JefersonHernandez00/Sistema-Nivel-Y-Temperatura/img y video/ensamblaje 2.JPG

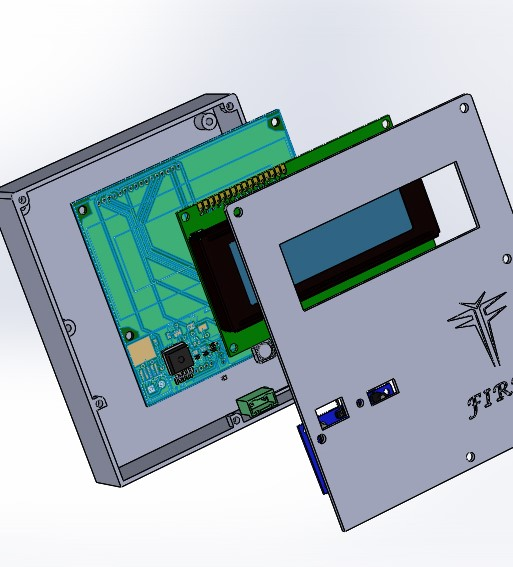
img y video/ensamblaje 2.JPG
