JefersonHernandez00/Sistema-Nivel-Y-Temperatura/img y video/Ensamblaje carcasa t.jpg

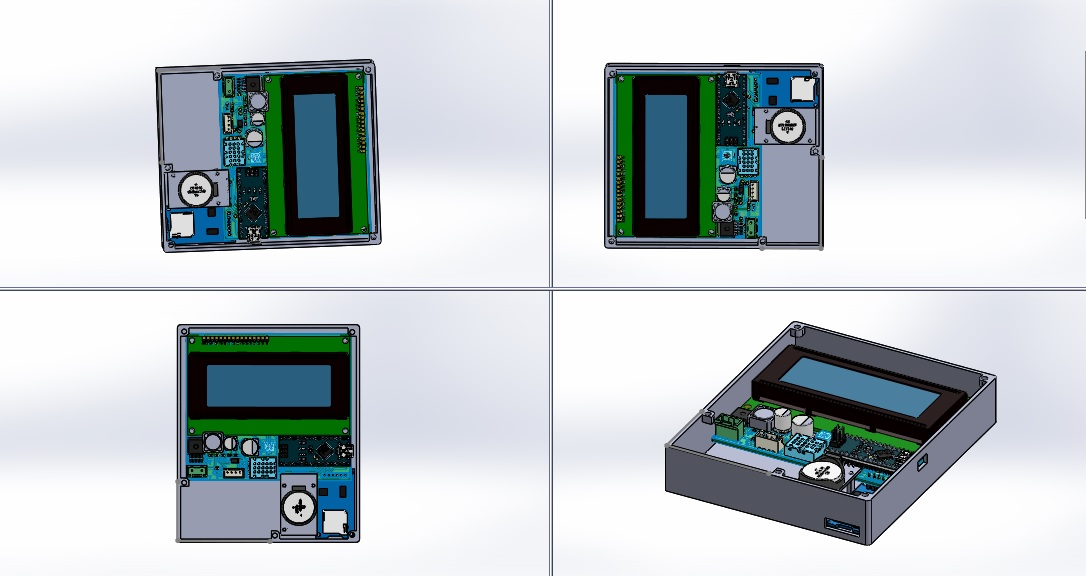
img y video/Ensamblaje carcasa t.jpg
