JefersonHernandez00/Sistema-Nivel-Y-Temperatura/img y video/.png

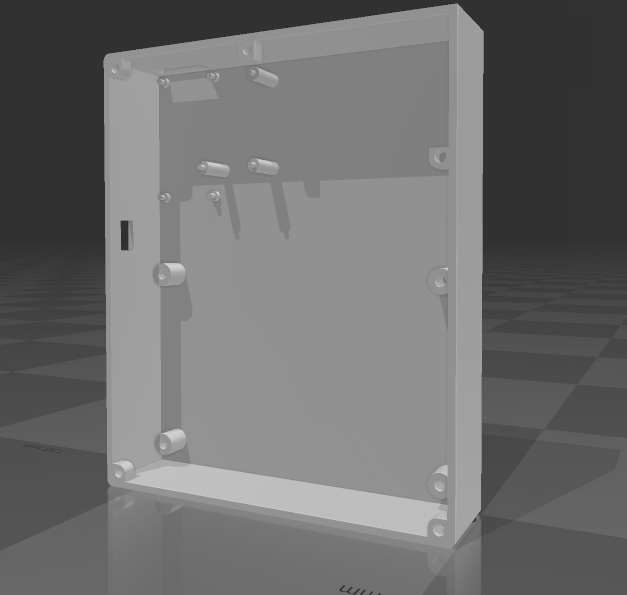
img y video/.png
