JefersonHernandez00/Sistema-Nivel-Y-Temperatura/img y video/Carcasa medidor de  nivel t.jpg

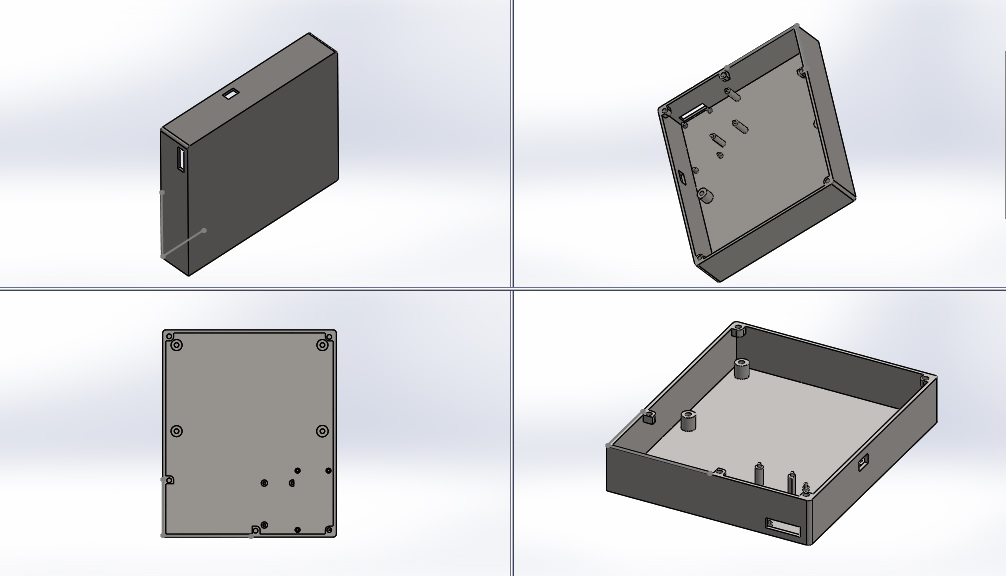
img y video/Carcasa medidor de nivel t.jpg
