JefersonHernandez00/Sistema-Nivel-Y-Temperatura/img y video/Carcasa medidor de  nivel.JPG

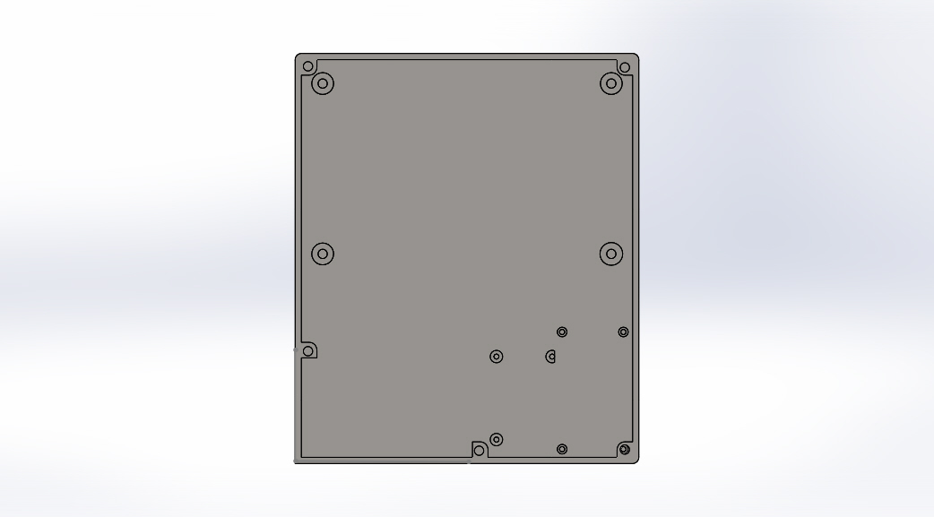
img y video/Carcasa medidor de nivel.JPG
