JefersonHernandez00/Sistema-Nivel-Y-Temperatura/img y video/cc.JPG

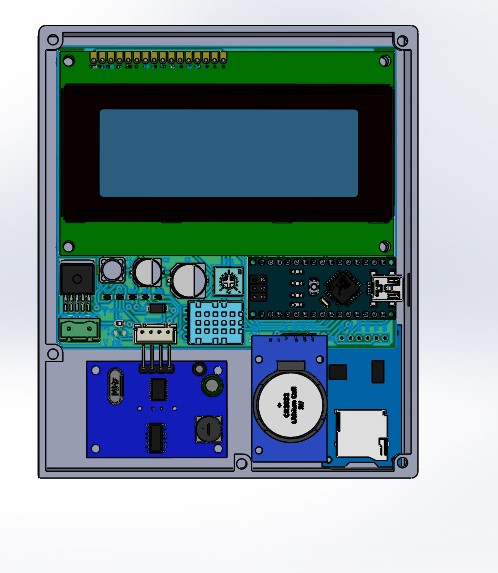
img y video/cc.JPG
