JefersonHernandez00/Sistema-Nivel-Y-Temperatura/img y video/esquematico.png

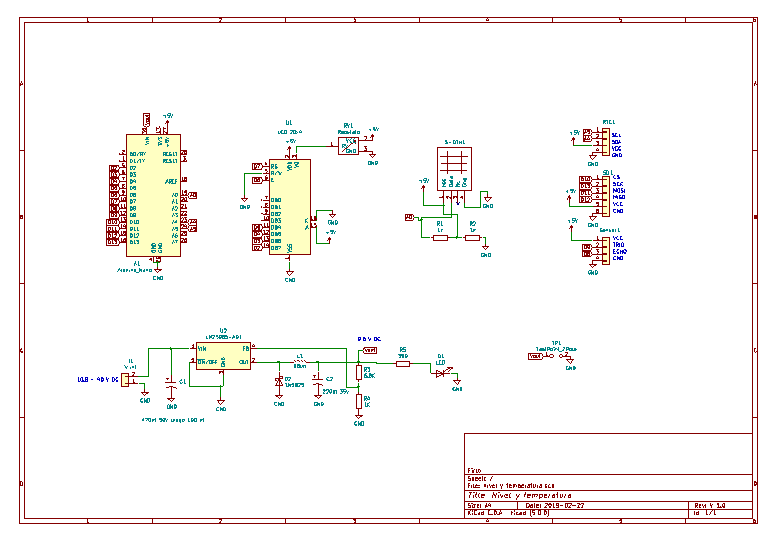
img y video/esquematico.png
