JefersonHernandez00/Sistema-Nivel-Y-Temperatura/img y video/IMG-20190923-WA0002.jpeg

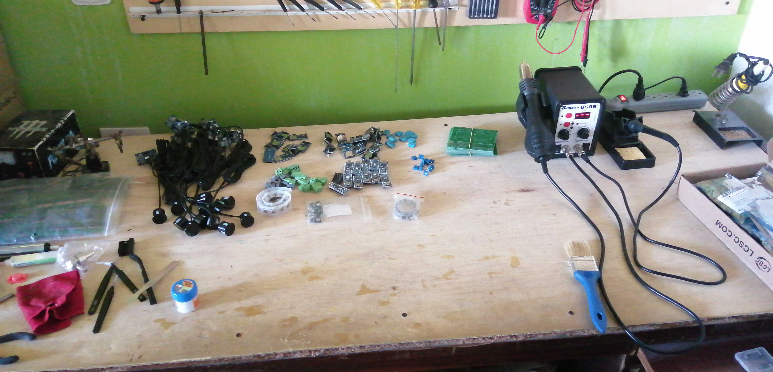
img y video/IMG-20190923-WA0002.jpeg
