JefersonHernandez00/Sistema-Nivel-Y-Temperatura/img y video/IMG-20190927-WA0010.jpg

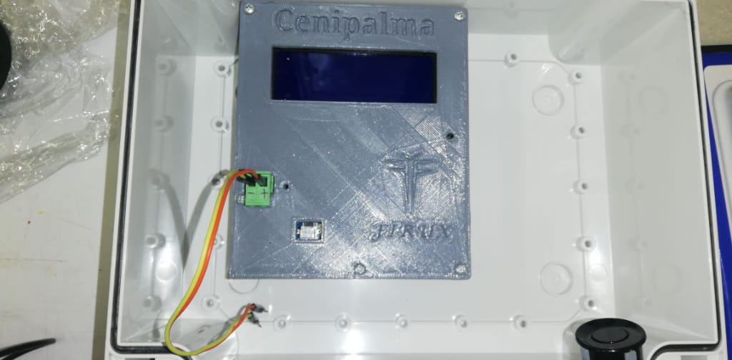
img y video/IMG-20190927-WA0010.jpg
