JefersonHernandez00/Sistema-Nivel-Y-Temperatura/img y video/IMG-20191017-WA0028.jpg

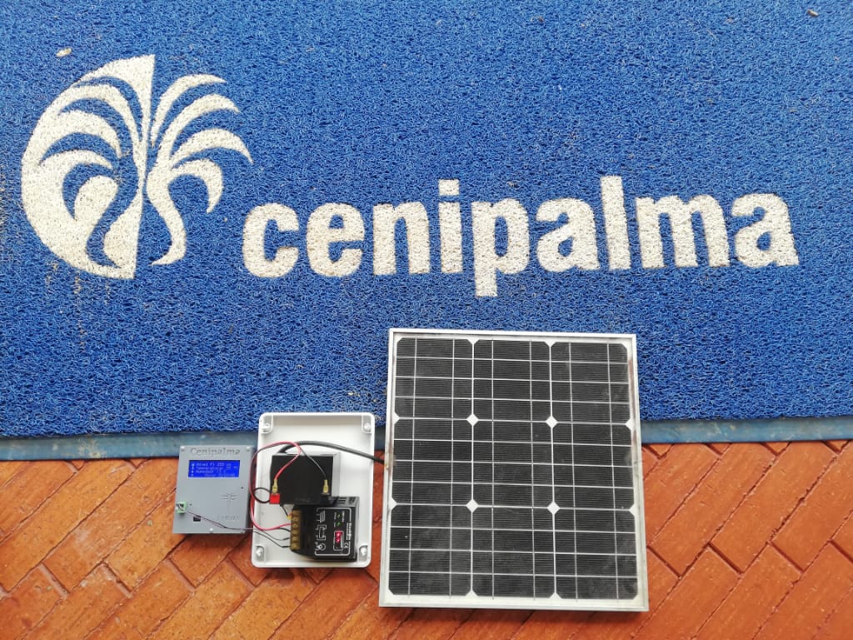
img y video/IMG-20191017-WA0028.jpg
