JefersonHernandez00/Sistema-Nivel-Y-Temperatura/img y video/IMG-20191017-WA0040.jpg

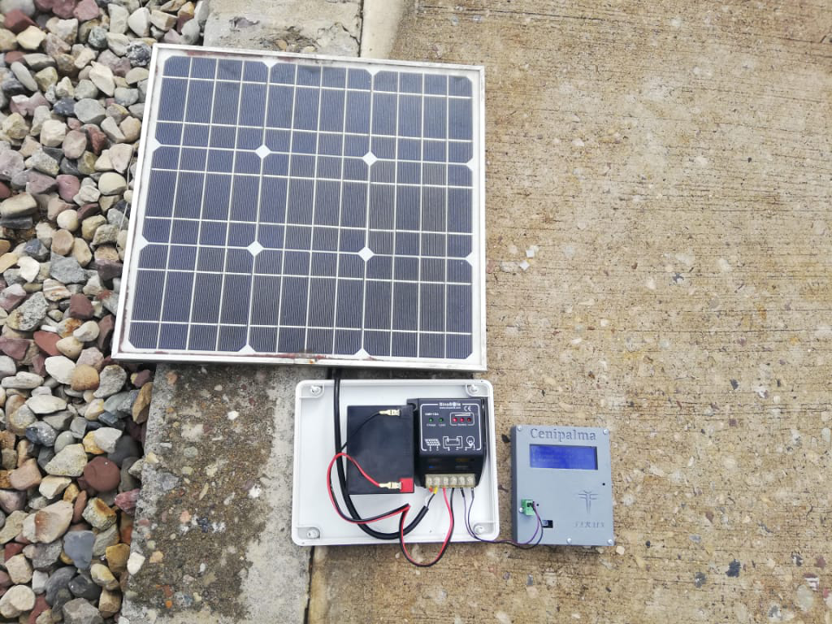
img y video/IMG-20191017-WA0040.jpg
