JefersonHernandez00/Sistema-Nivel-Y-Temperatura/img y video/IMG-20191018-WA0004.jpg

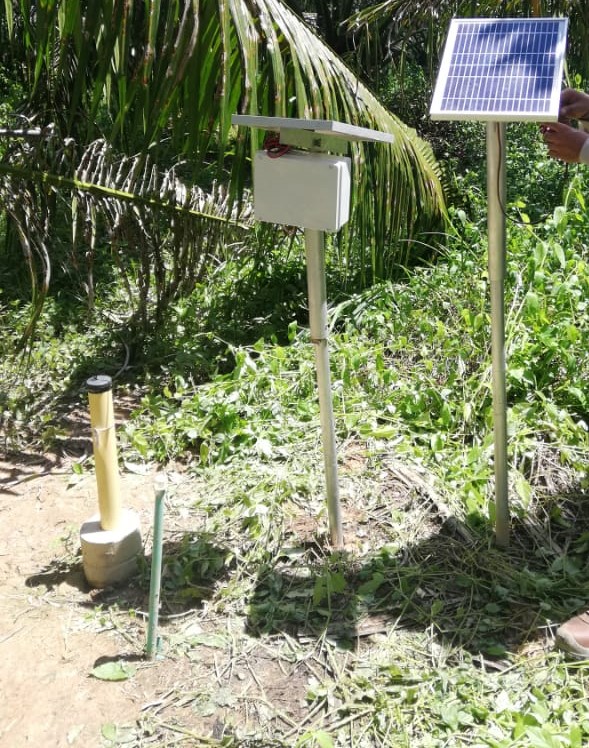
img y video/IMG-20191018-WA0004.jpg
