JefersonHernandez00/Sistema-Nivel-Y-Temperatura/img y video/IMG_20190506_111647.jpg

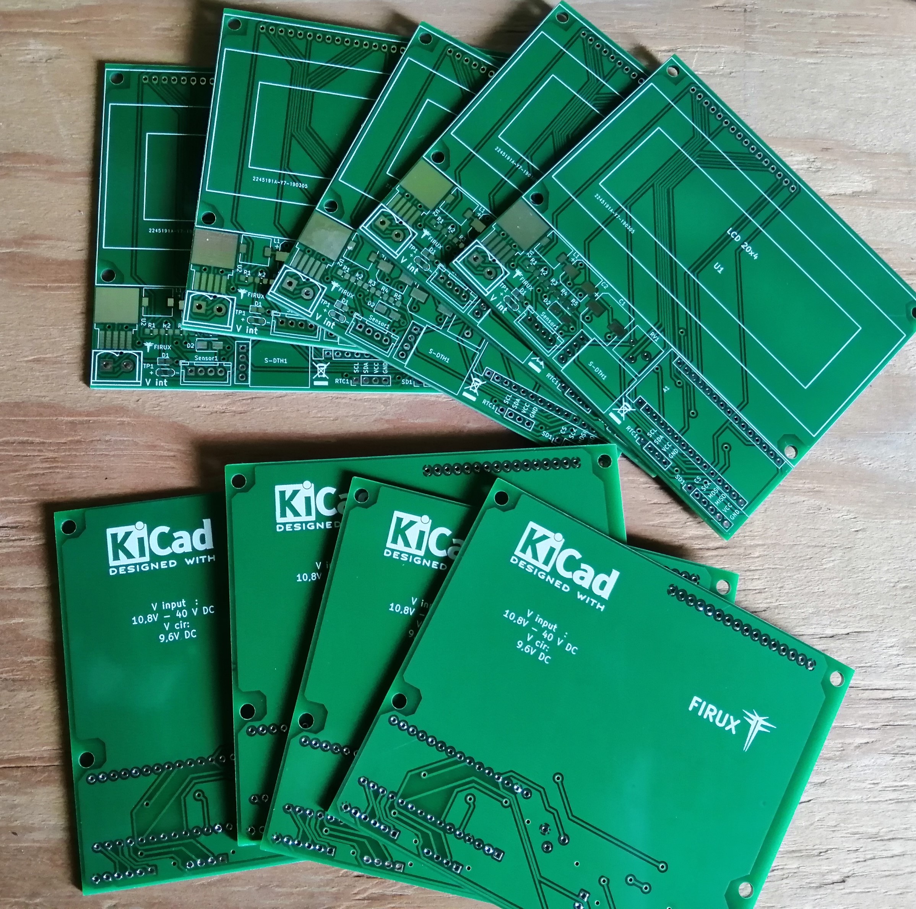
img y video/IMG_20190506_111647.jpg
