JefersonHernandez00/Sistema-Nivel-Y-Temperatura/img y video/IMG_20190611_220659.jpg

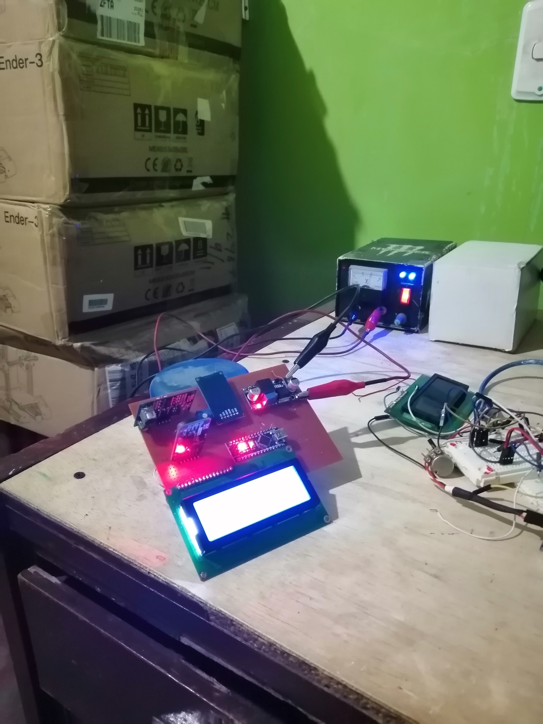
img y video/IMG_20190611_220659.jpg
