JefersonHernandez00/Sistema-Nivel-Y-Temperatura/img y video/IMG_20190923_133339.jpg

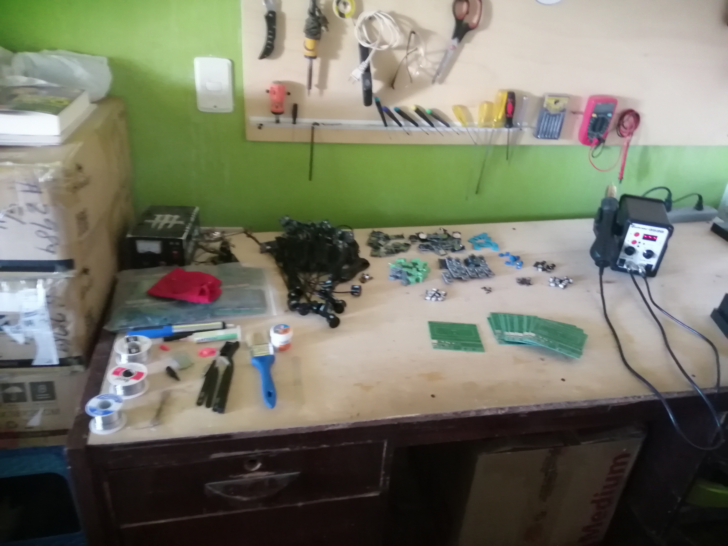
img y video/IMG_20190923_133339.jpg
