JefersonHernandez00/Sistema-Nivel-Y-Temperatura/img y video/IMG_20190923_155856.jpg

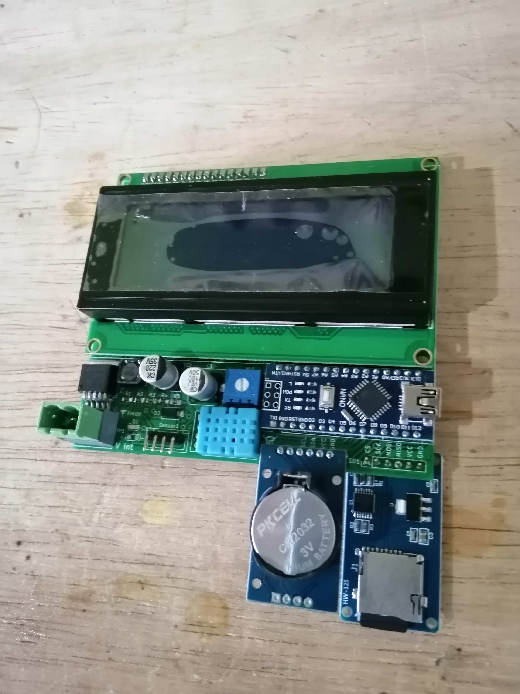
img y video/IMG_20190923_155856.jpg
