JefersonHernandez00/Sistema-Nivel-Y-Temperatura/img y video/IMG_20190923_161401.jpg

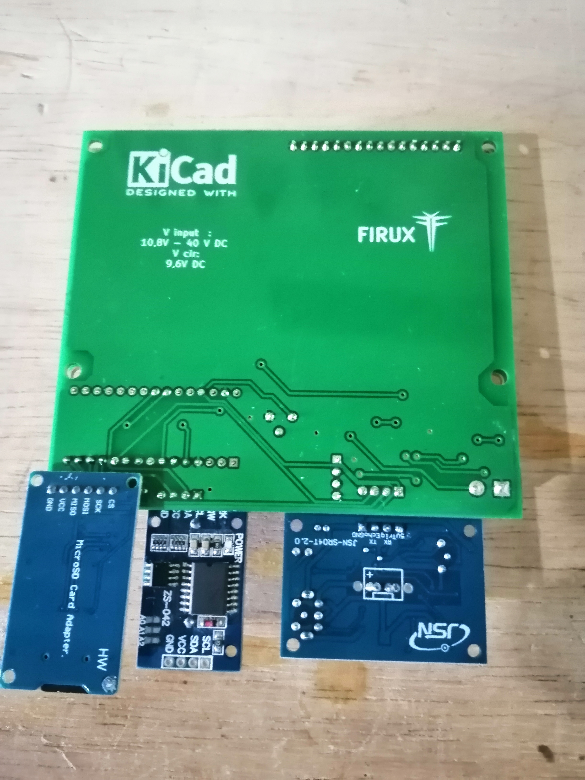
img y video/IMG_20190923_161401.jpg
