JefersonHernandez00/Sistema-Nivel-Y-Temperatura/img y video/IMG_20190923_161447.jpg

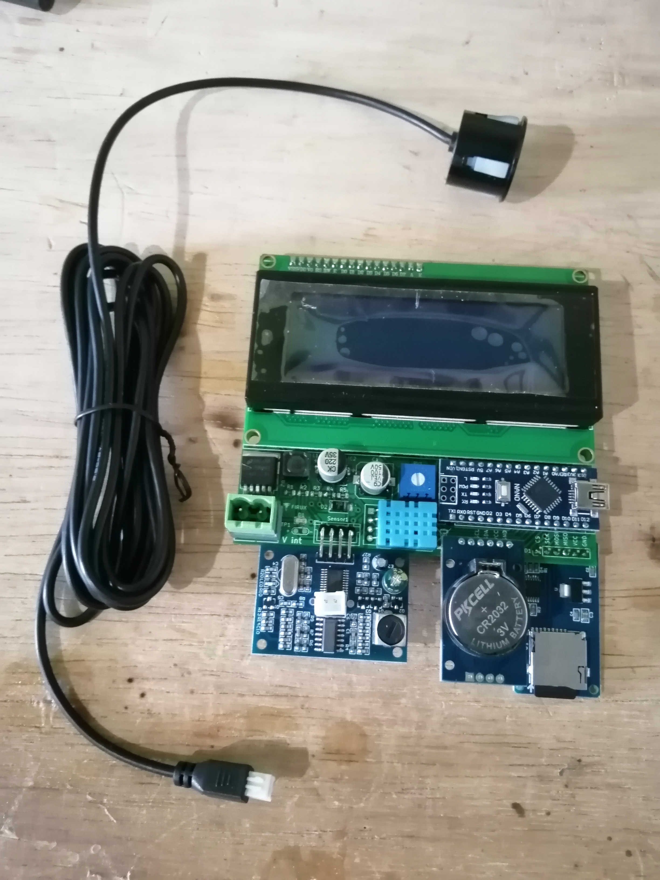
img y video/IMG_20190923_161447.jpg
