JefersonHernandez00/Sistema-Nivel-Y-Temperatura/img y video/IMG_20190923_162317.jpg

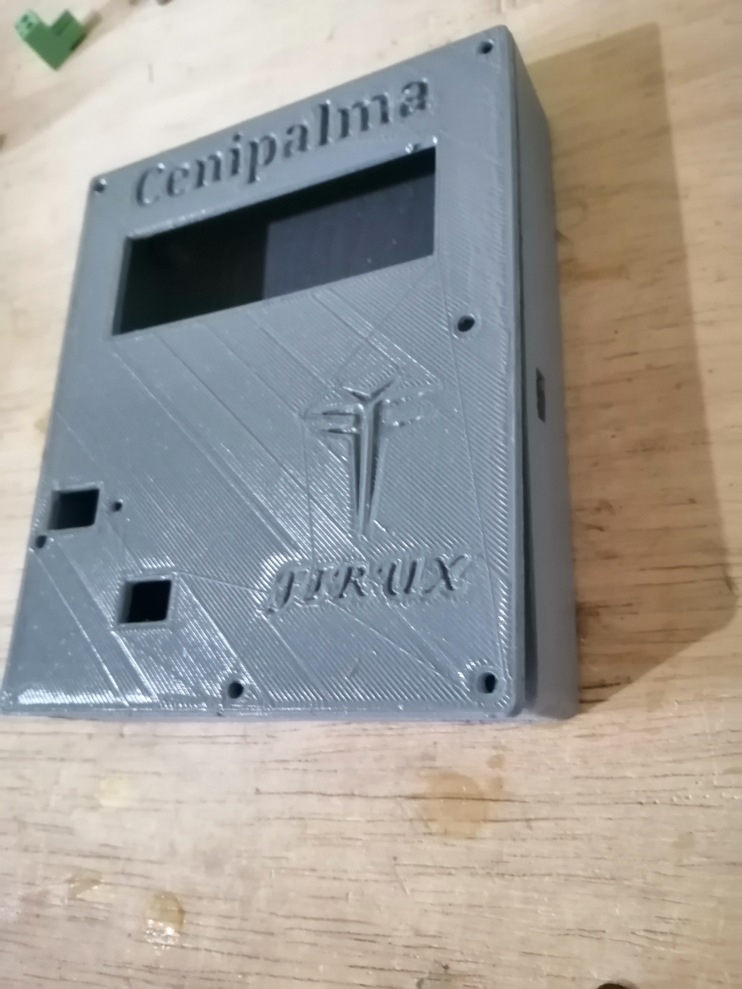
img y video/IMG_20190923_162317.jpg
