JefersonHernandez00/Sistema-Nivel-Y-Temperatura/img y video/IMG_20190924_174015.jpg

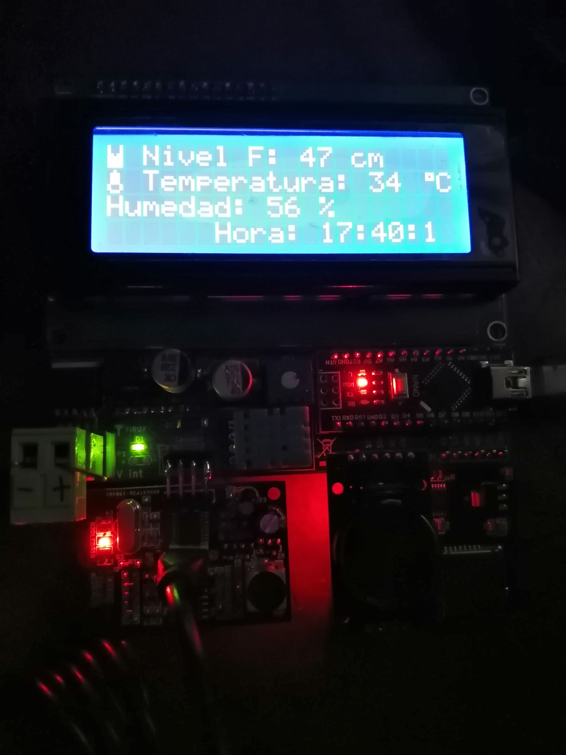
img y video/IMG_20190924_174015.jpg
