JefersonHernandez00/Sistema-Nivel-Y-Temperatura/img y video/IMG_20190924_174020.jpg

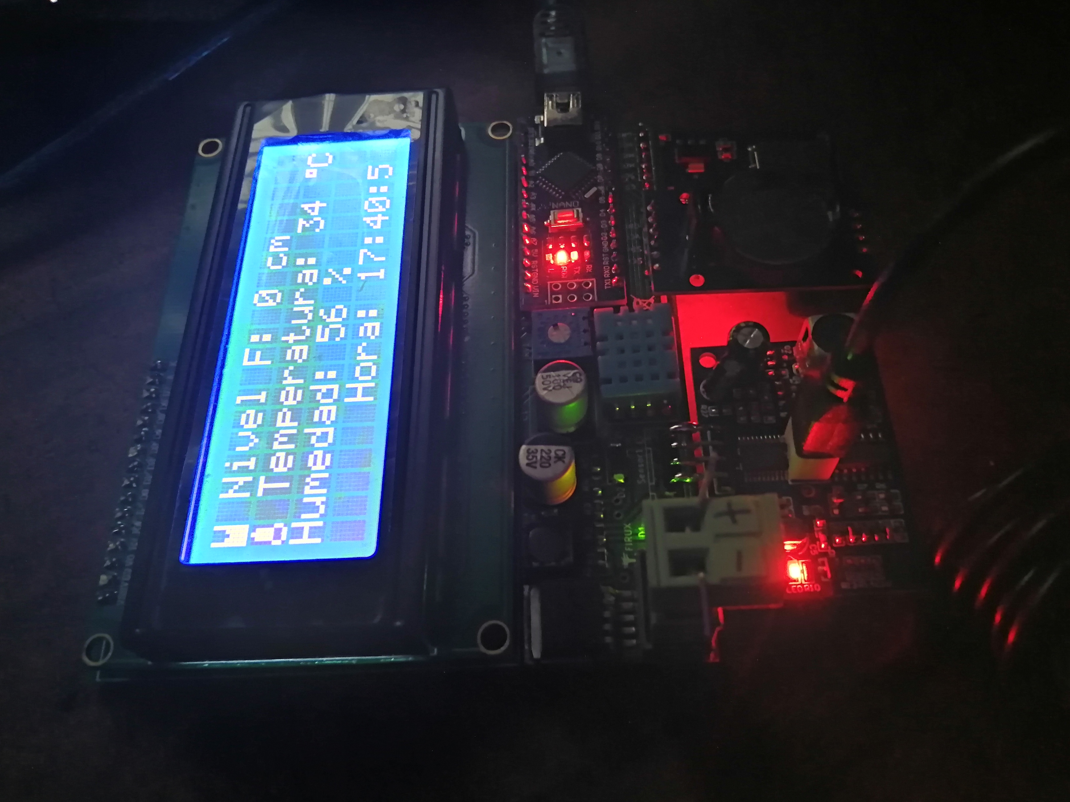
img y video/IMG_20190924_174020.jpg
