JefersonHernandez00/Sistema-Nivel-Y-Temperatura/img y video/IMG_20190924_174026.jpg

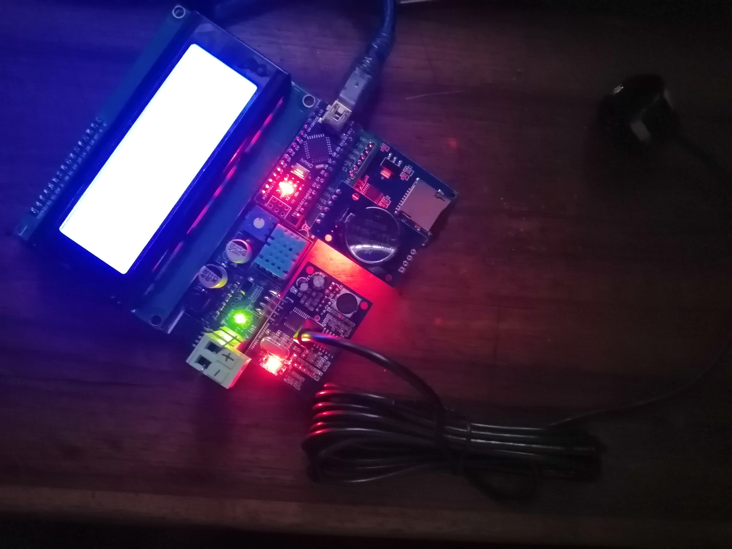
img y video/IMG_20190924_174026.jpg
