JefersonHernandez00/Sistema-Nivel-Y-Temperatura/img y video/IMG_20190925_163047.jpg

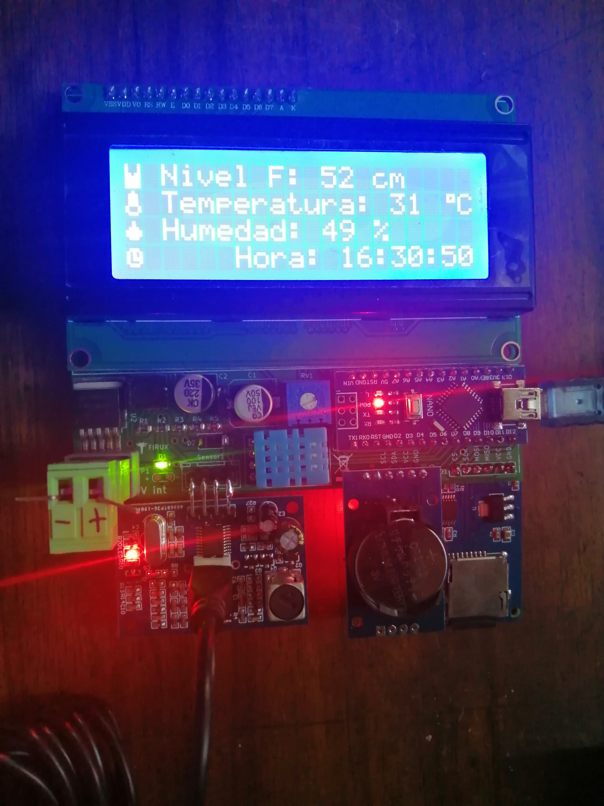
img y video/IMG_20190925_163047.jpg
