JefersonHernandez00/Sistema-Nivel-Y-Temperatura/img y video/IMG_20190926_141606 - copia.jpg

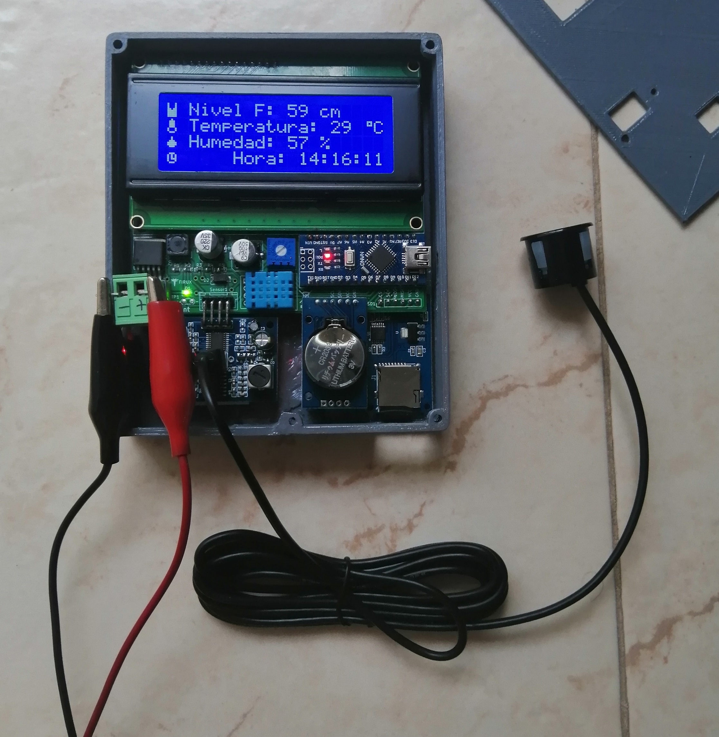
img y video/IMG_20190926_141606 - copia.jpg
