JefersonHernandez00/Sistema-Nivel-Y-Temperatura/img y video/IMG_20190926_164123.jpg

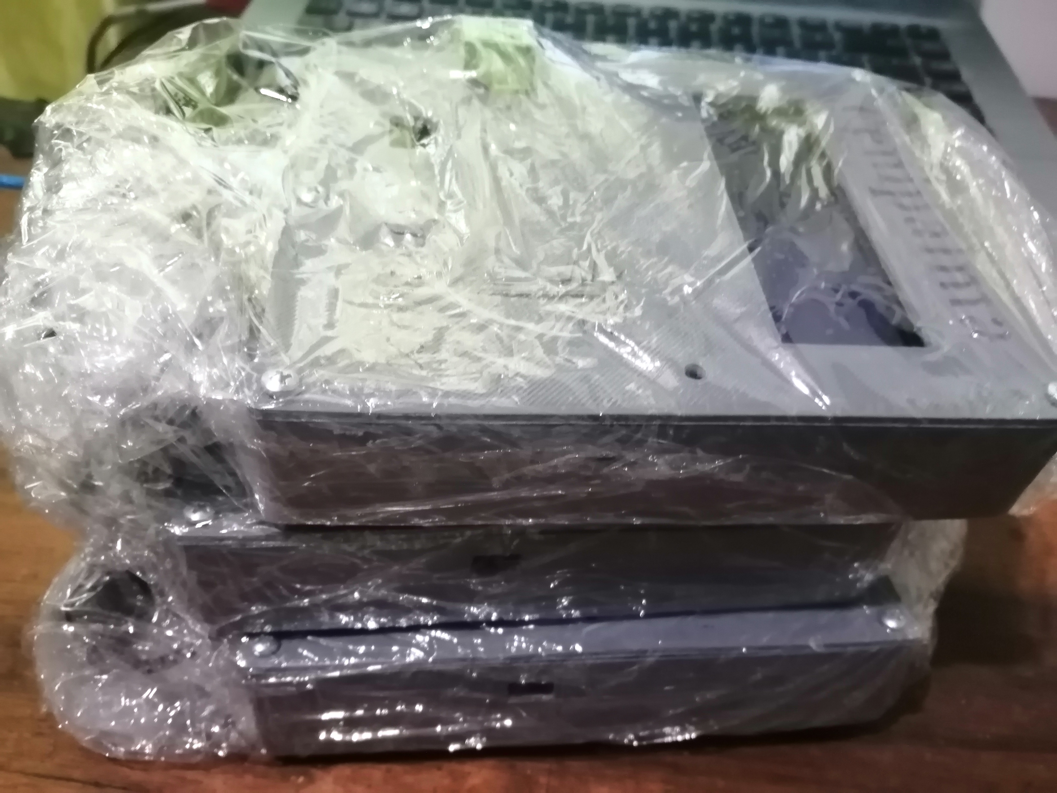
img y video/IMG_20190926_164123.jpg
