JefersonHernandez00/Sistema-Nivel-Y-Temperatura/img y video/IMG_20190929_165953.jpg

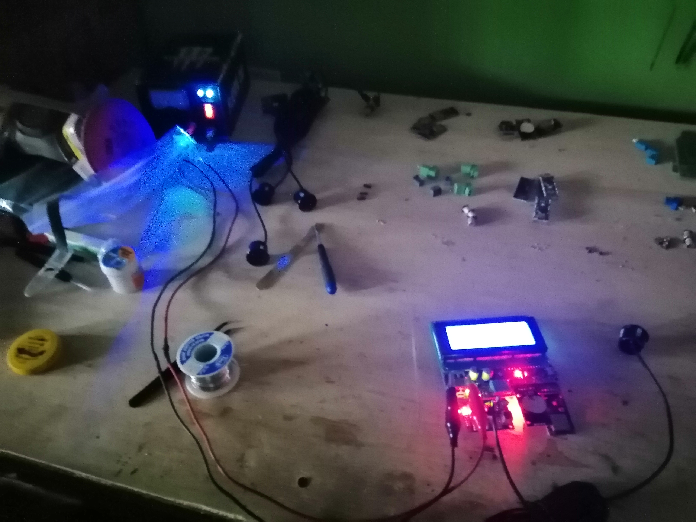
img y video/IMG_20190929_165953.jpg
