JefersonHernandez00/Sistema-Nivel-Y-Temperatura/img y video/IMG_20190929_170008.jpg

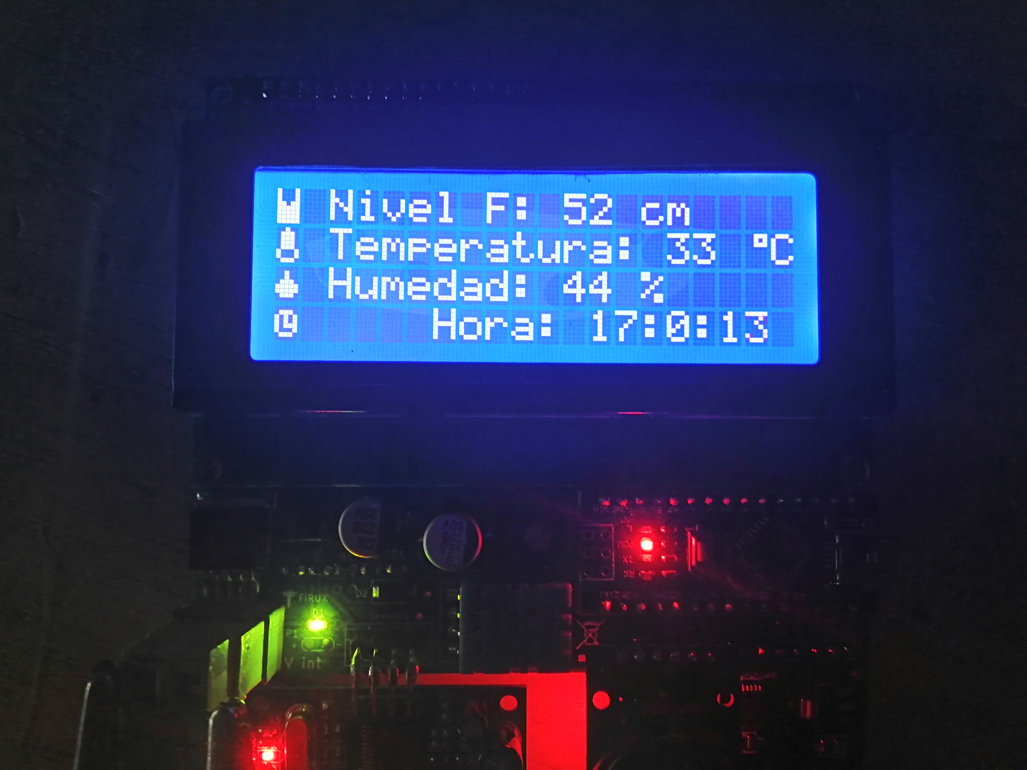
img y video/IMG_20190929_170008.jpg
