JefersonHernandez00/Sistema-Nivel-Y-Temperatura/img y video/IMG_20190930_161801.jpg

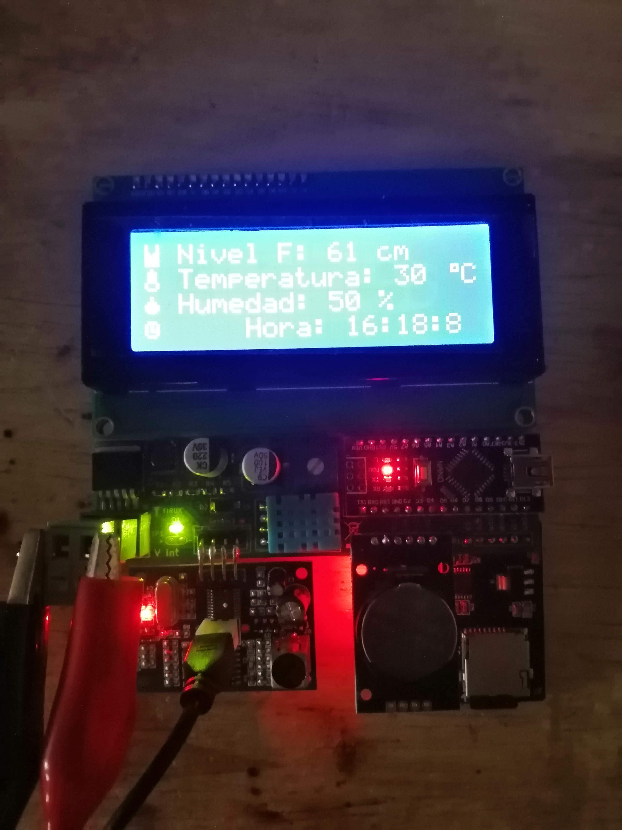
img y video/IMG_20190930_161801.jpg
