JefersonHernandez00/Sistema-Nivel-Y-Temperatura/img y video/IMG_20191001_193928.jpg

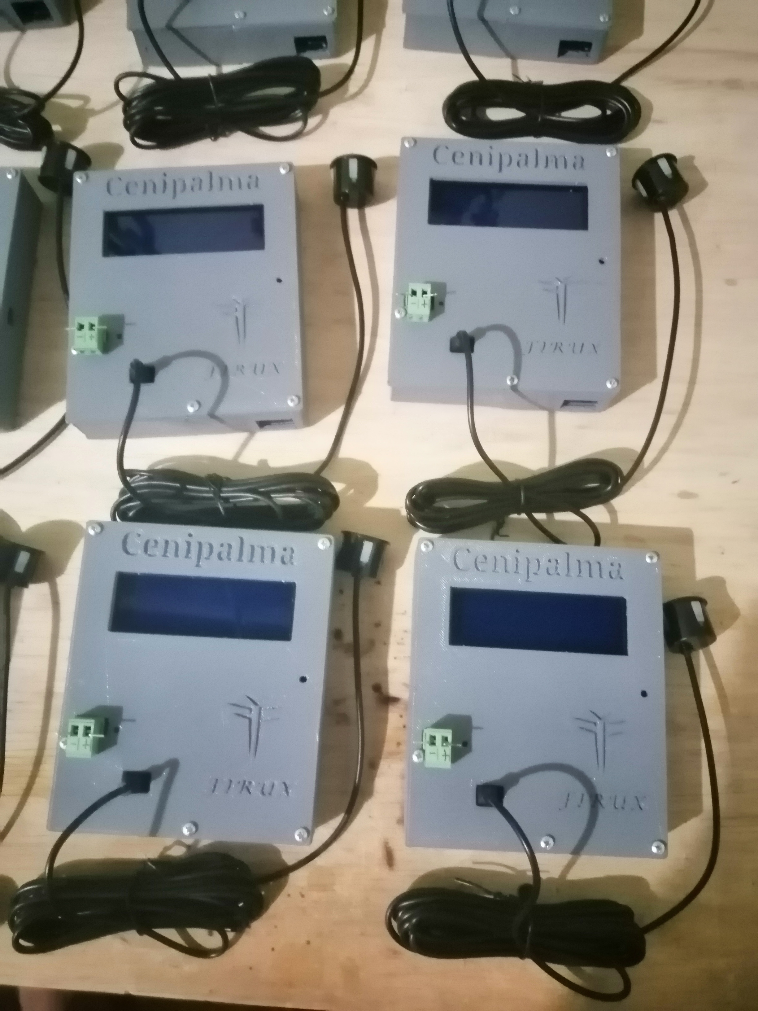
img y video/IMG_20191001_193928.jpg
