JefersonHernandez00/Sistema-Nivel-Y-Temperatura/img y video/IMG_20191001_220516.jpg

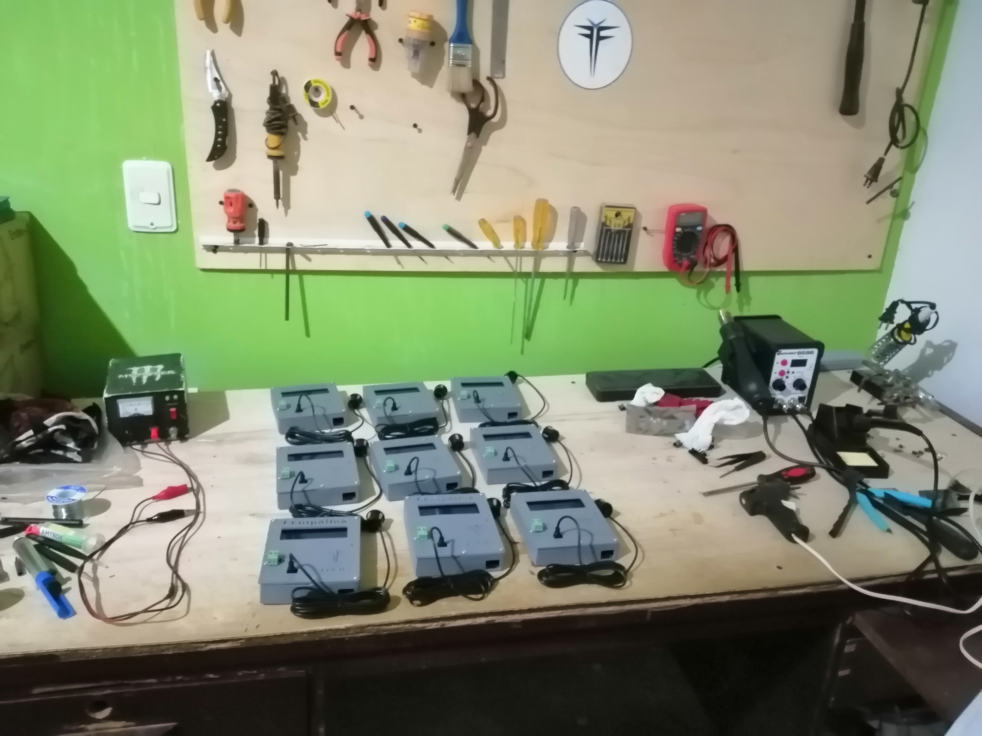
img y video/IMG_20191001_220516.jpg
