JefersonHernandez00/Sistema-Nivel-Y-Temperatura/img y video/IMG_20191002_113729.jpg

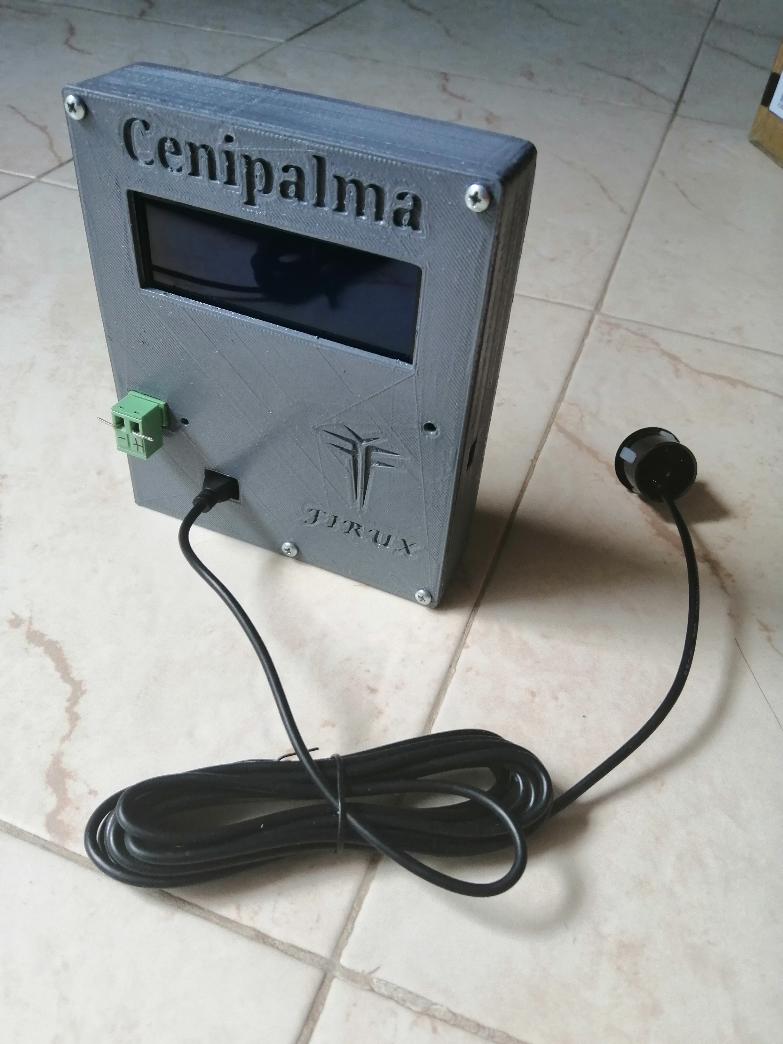
img y video/IMG_20191002_113729.jpg
