JefersonHernandez00/Sistema-Nivel-Y-Temperatura/img y video/IMG_20191002_113740.jpg

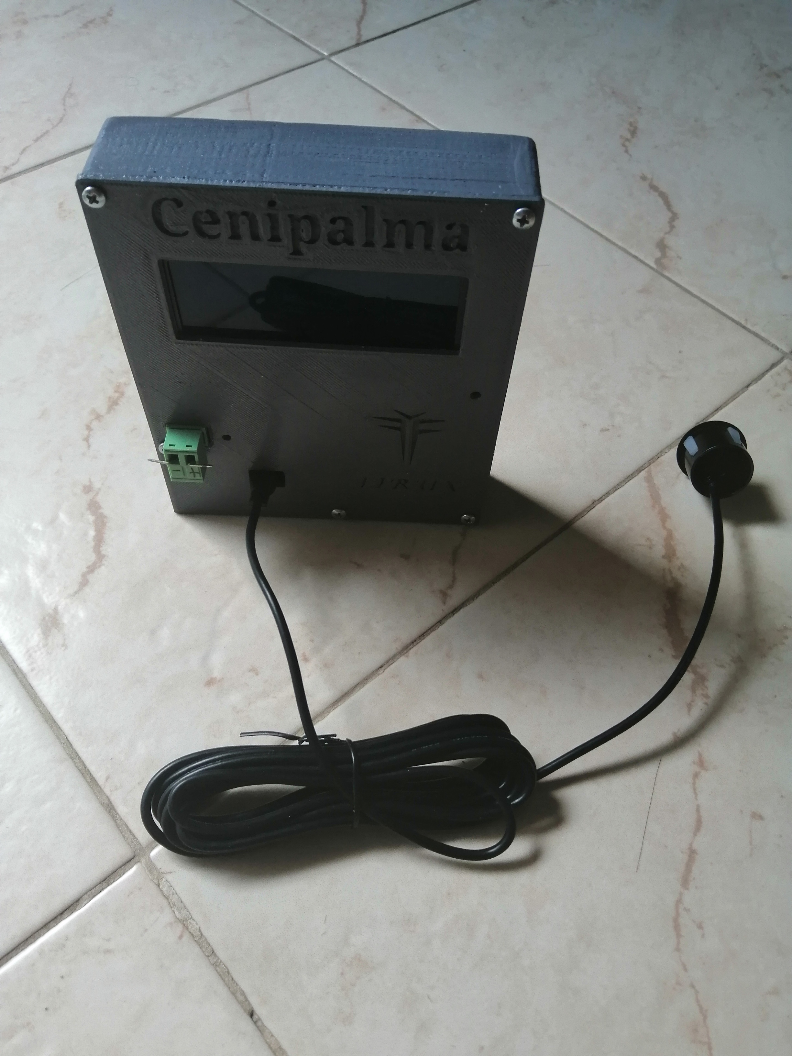
img y video/IMG_20191002_113740.jpg
