JefersonHernandez00/Sistema-Nivel-Y-Temperatura/img y video/pcb1.png

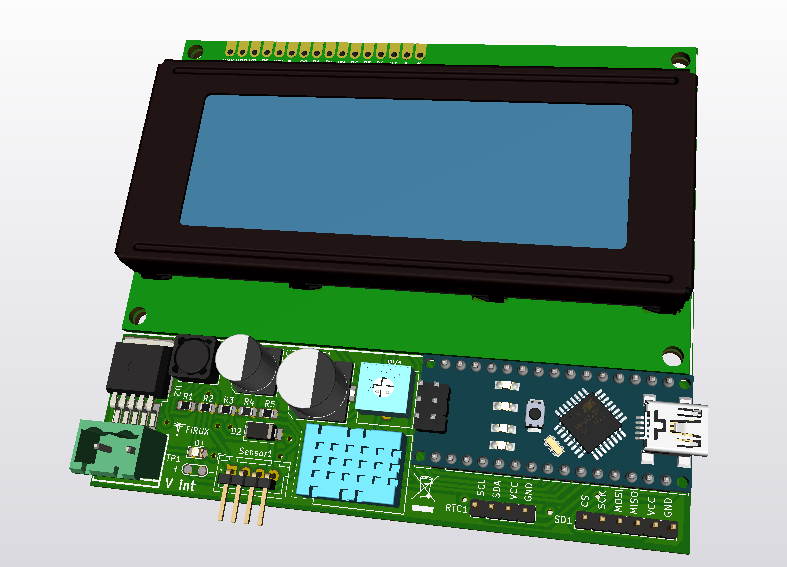
img y video/pcb1.png
