JefersonHernandez00/Sistema-Nivel-Y-Temperatura/img y video/pcb2.png

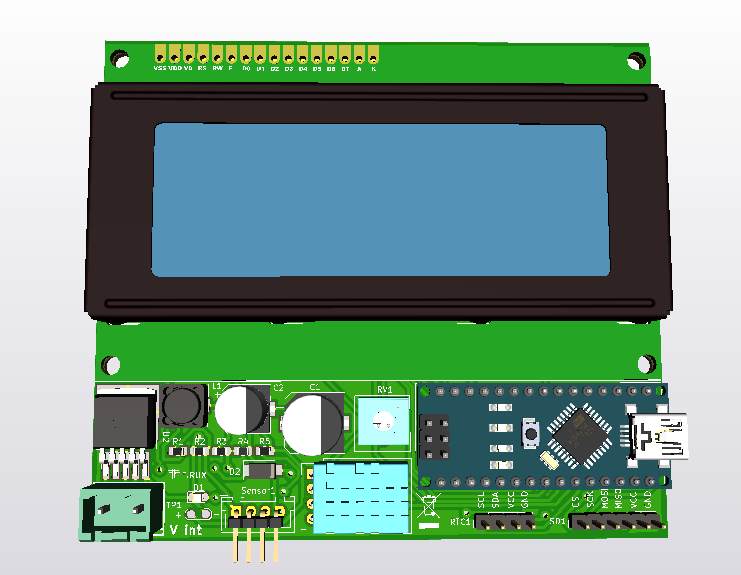
img y video/pcb2.png
