JefersonHernandez00/Sistema-Nivel-Y-Temperatura/img y video/pcb3.png

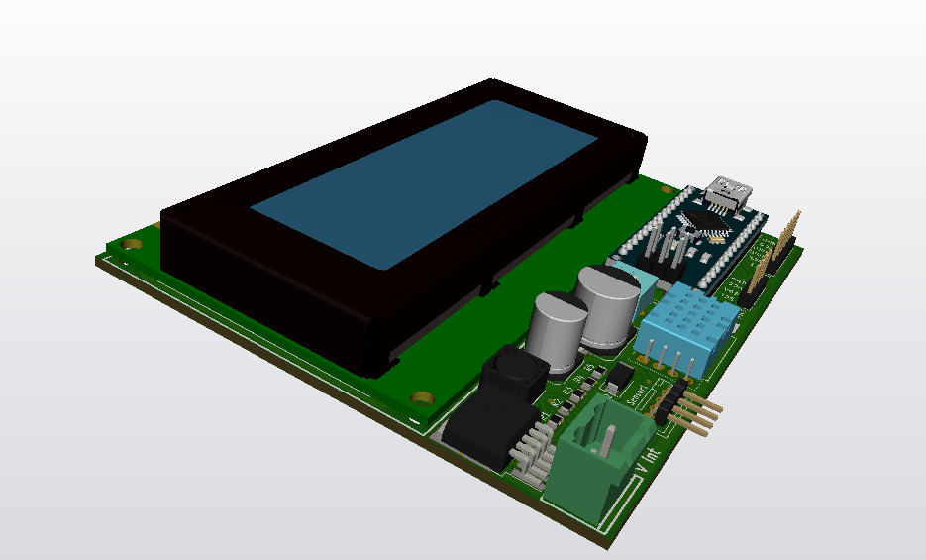
img y video/pcb3.png
