JefersonHernandez00/Sistema-Nivel-Y-Temperatura/img y video/pcb4.png

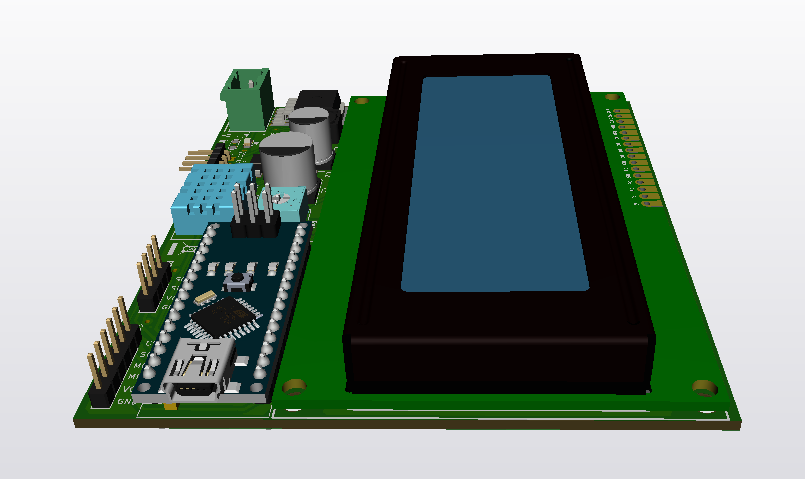
img y video/pcb4.png
