JefersonHernandez00/Sistema-Nivel-Y-Temperatura/img y video/pcb5.png

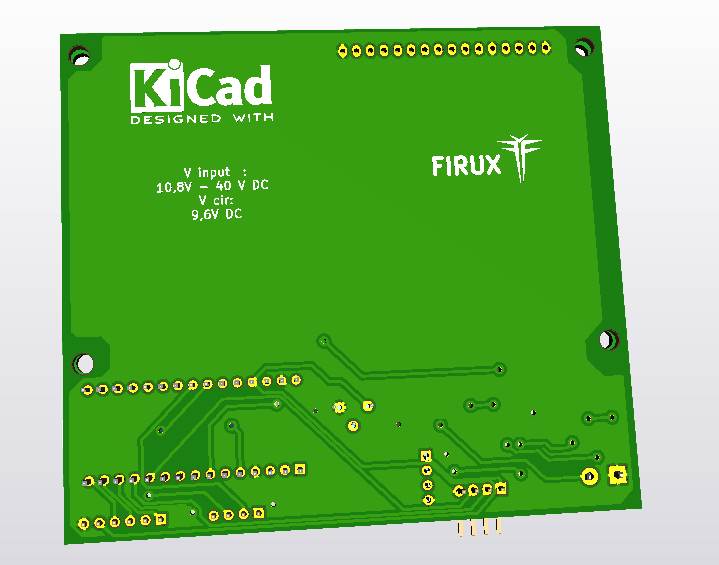
img y video/pcb5.png
