JefersonHernandez00/Sistema-Nivel-Y-Temperatura/img y video/pcb6.png

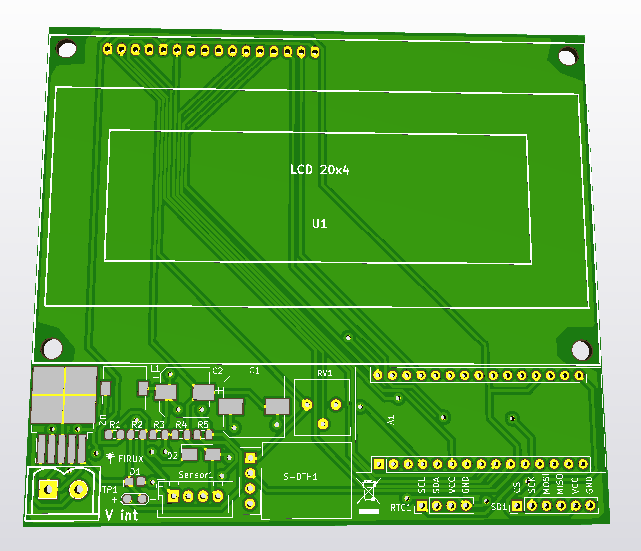
img y video/pcb6.png
