JefersonHernandez00/Sistema-Nivel-Y-Temperatura/img y video/pcb7.png

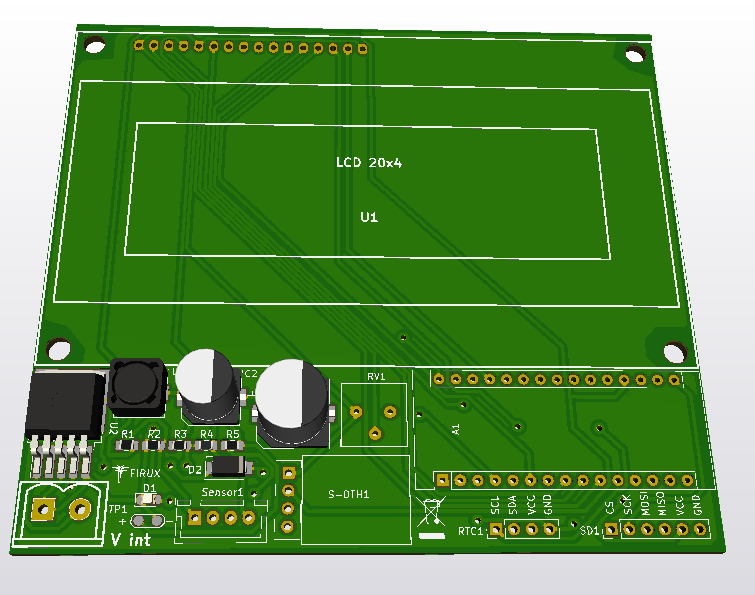
img y video/pcb7.png
