JefersonHernandez00/Sistema-Nivel-Y-Temperatura/img y video/pcb8.png

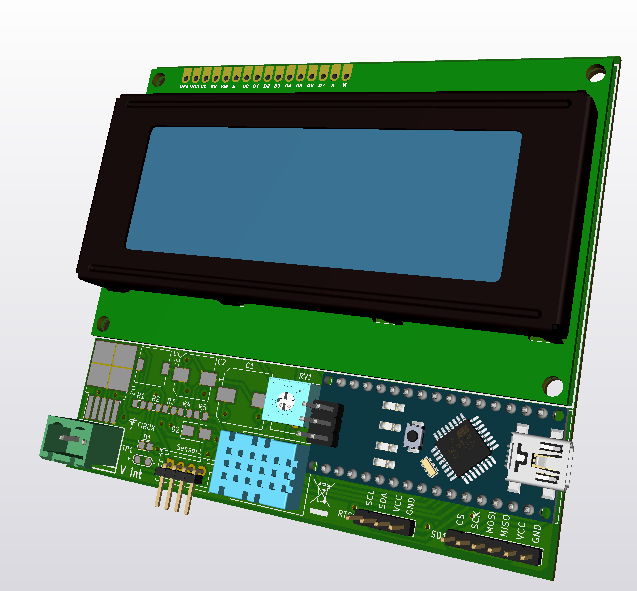
img y video/pcb8.png
