JefersonHernandez00/Sistema-Nivel-Y-Temperatura/img y video/pcb9.png

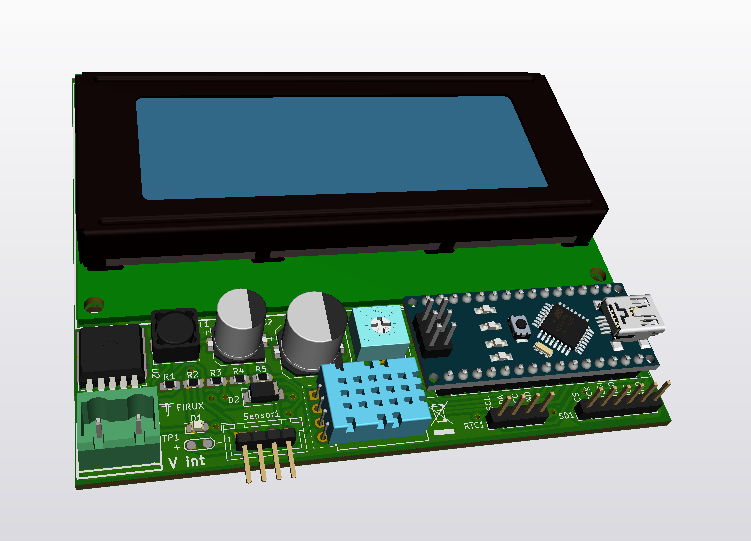
img y video/pcb9.png
