JefersonHernandez00/Sistema-Nivel-Y-Temperatura/img y video/pcb.png

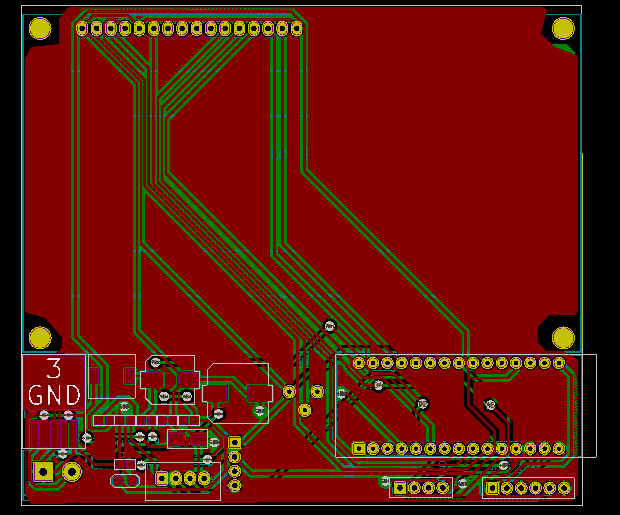
img y video/pcb.png
