JefersonHernandez00/Sistema-Nivel-Y-Temperatura/img y video/proyecto firux pcb 2.JPG

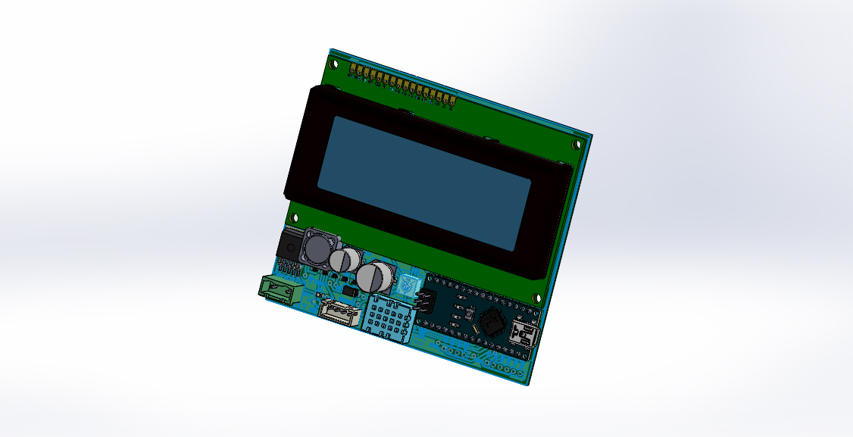
img y video/proyecto firux pcb 2.JPG
