JefersonHernandez00/Sistema-Nivel-Y-Temperatura/img y video/proyecto firux pcb 3.JPG

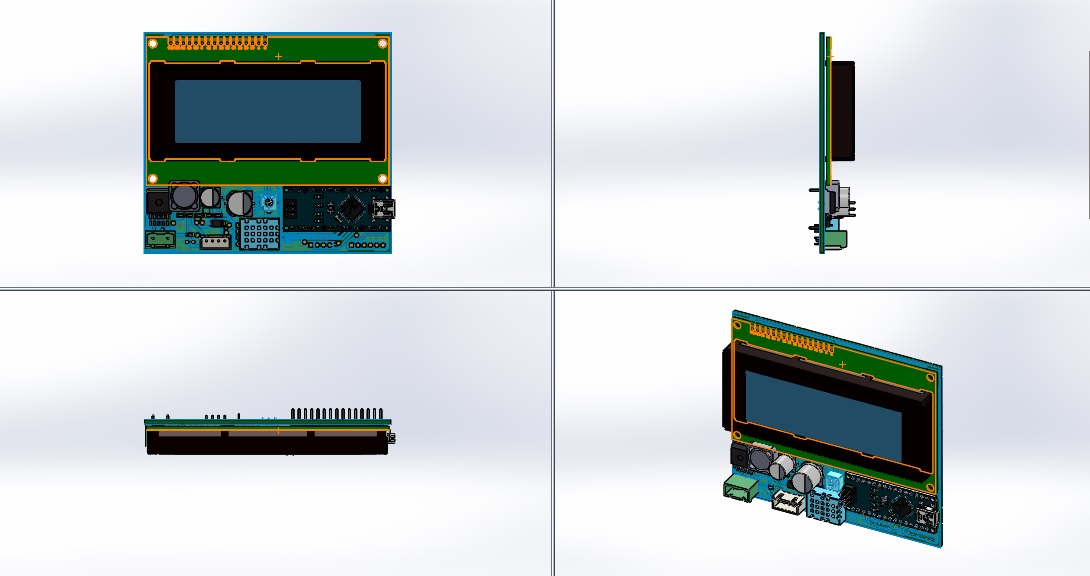
img y video/proyecto firux pcb 3.JPG
