JefersonHernandez00/Sistema-Nivel-Y-Temperatura/img y video/proyecto firux pcb.JPG

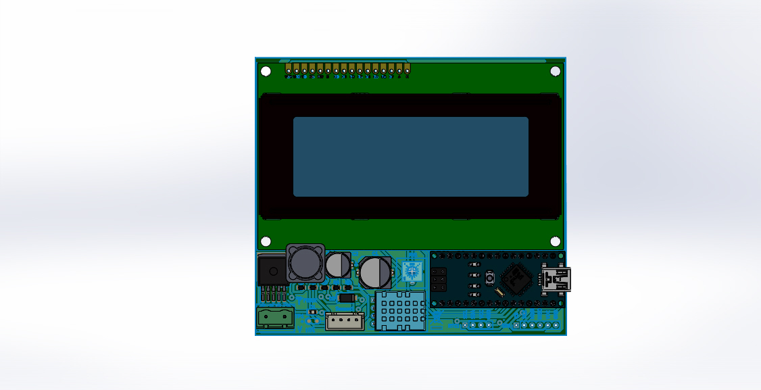
img y video/proyecto firux pcb.JPG
