JefersonHernandez00/Sistema-Nivel-Y-Temperatura/img y video/Tapa medidor de  nivel 2.JPG

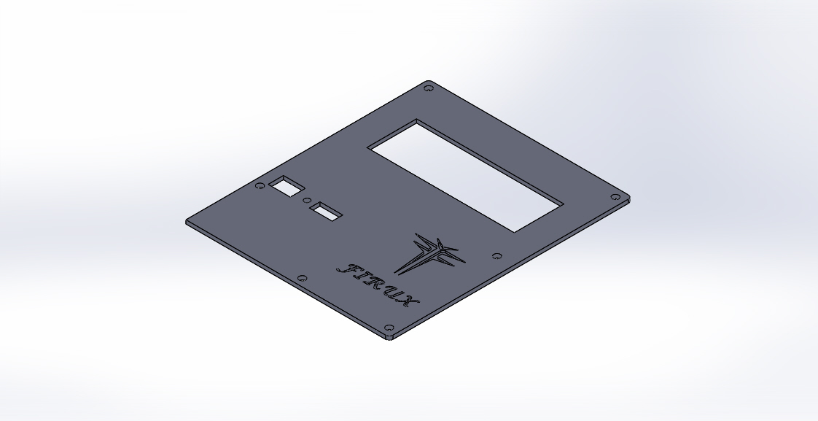
img y video/Tapa medidor de nivel 2.JPG
