JefersonHernandez00/Sistema-Nivel-Y-Temperatura/img y video/Tapa medidor de  nivel.JPG

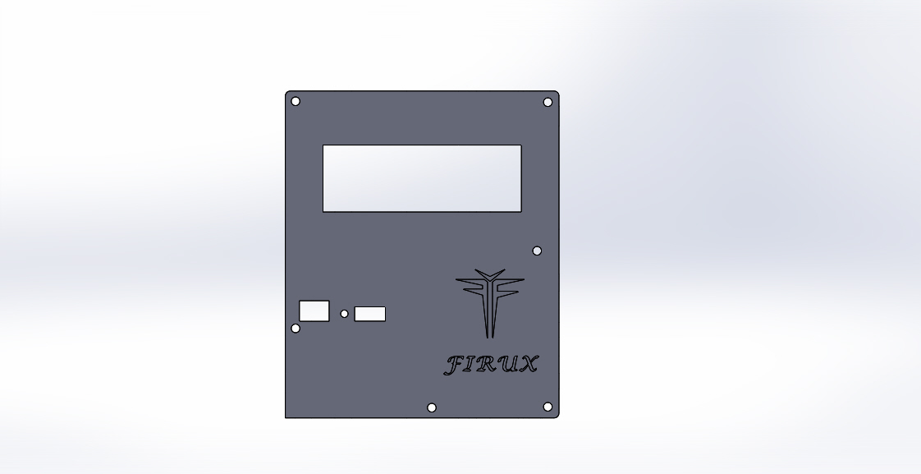
img y video/Tapa medidor de nivel.JPG
