JefersonHernandez00/Sistema-Nivel-Y-Temperatura/img y video/tapa proyecto cp.png

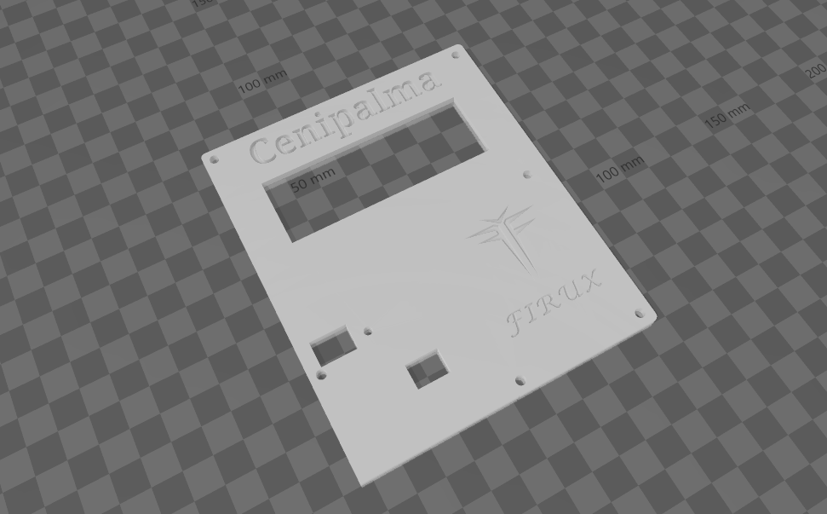
img y video/tapa proyecto cp.png
