JefersonHernandez00/Sistema-Nivel-Y-Temperatura/img y video/ensamblaje 3.png

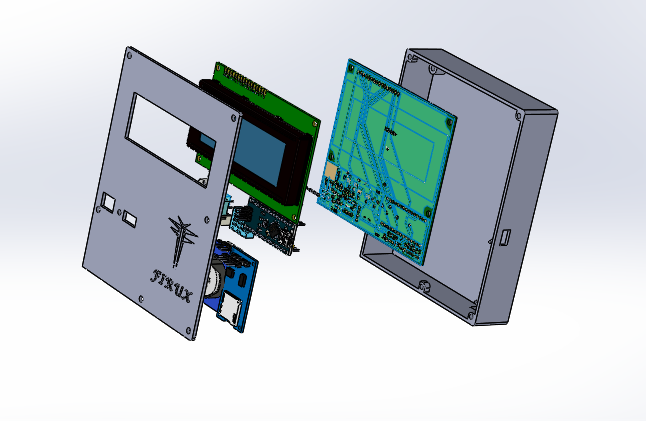
img y video/ensamblaje 3.png
