JefersonHernandez00/Sistema-Nivel-Y-Temperatura/img y video/Ensamblaje carcasa 3.JPG

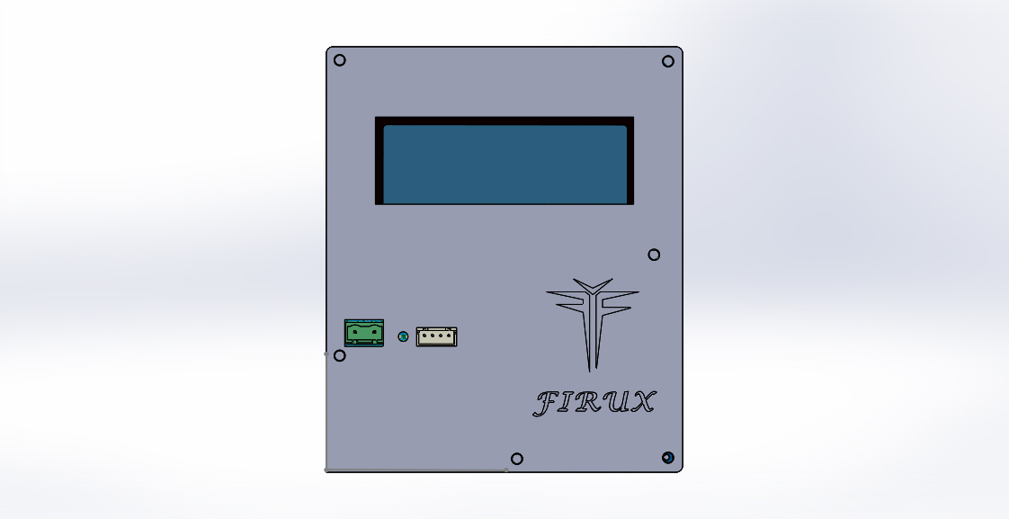
img y video/Ensamblaje carcasa 3.JPG
