JefersonHernandez00/Sistema-Nivel-Y-Temperatura/img y video/Ensamblaje carcasa 4.JPG

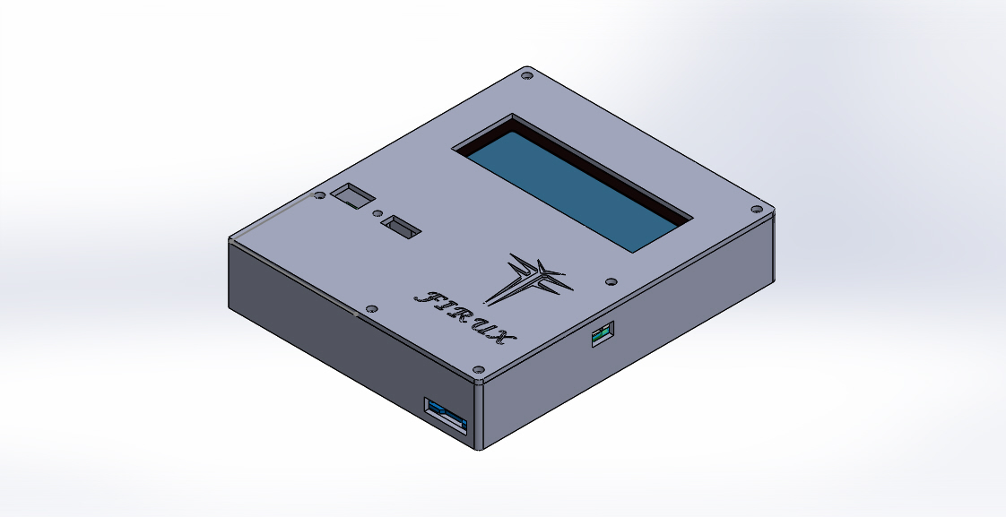
img y video/Ensamblaje carcasa 4.JPG
