JefersonHernandez00/Sistema-Nivel-Y-Temperatura/img y video/Ensamblaje carcasa.JPG

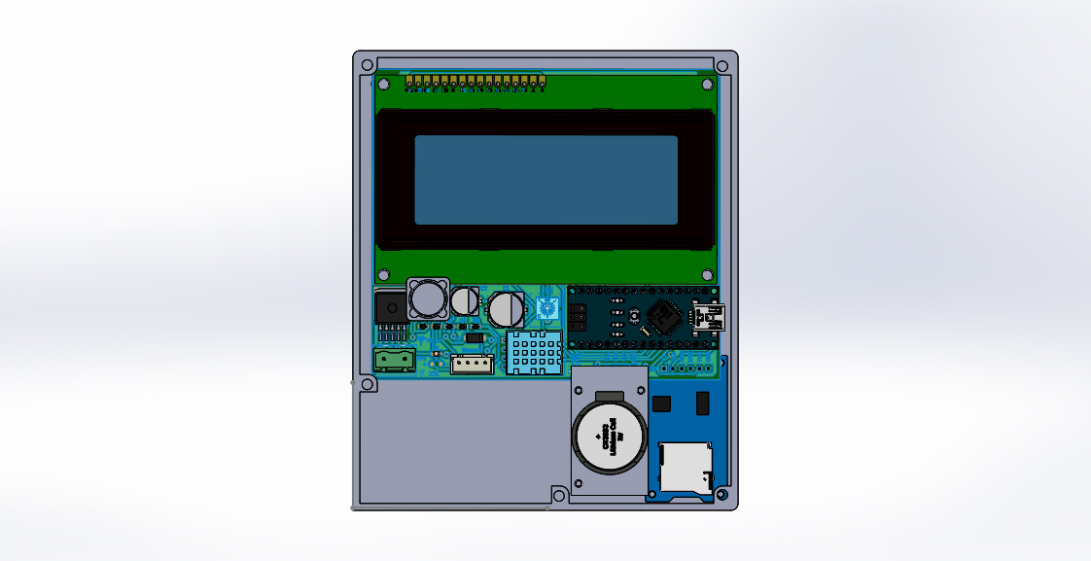
img y video/Ensamblaje carcasa.JPG
