JefersonHernandez00/Sistema-Nivel-Y-Temperatura/img y video/IMG-20190308-WA0014.jpeg

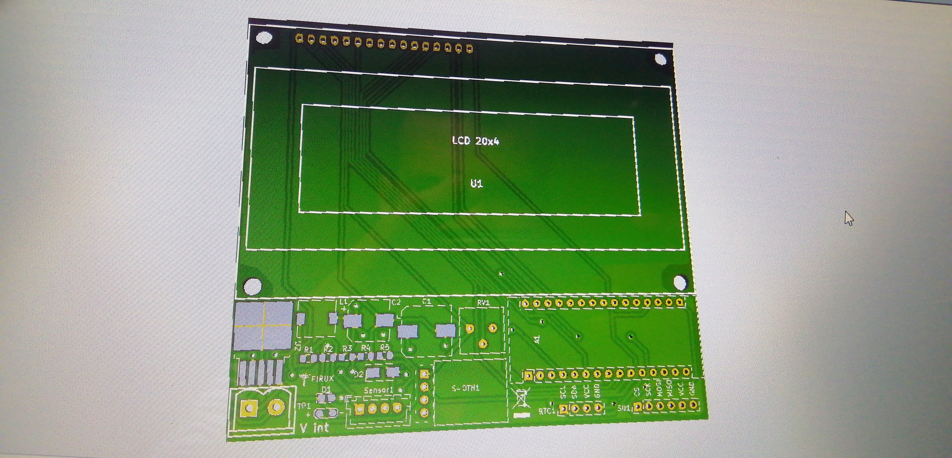
img y video/IMG-20190308-WA0014.jpeg
